tobi136B/co2-wall-sensor/docs/drawing/sheet2_adapters_de.png

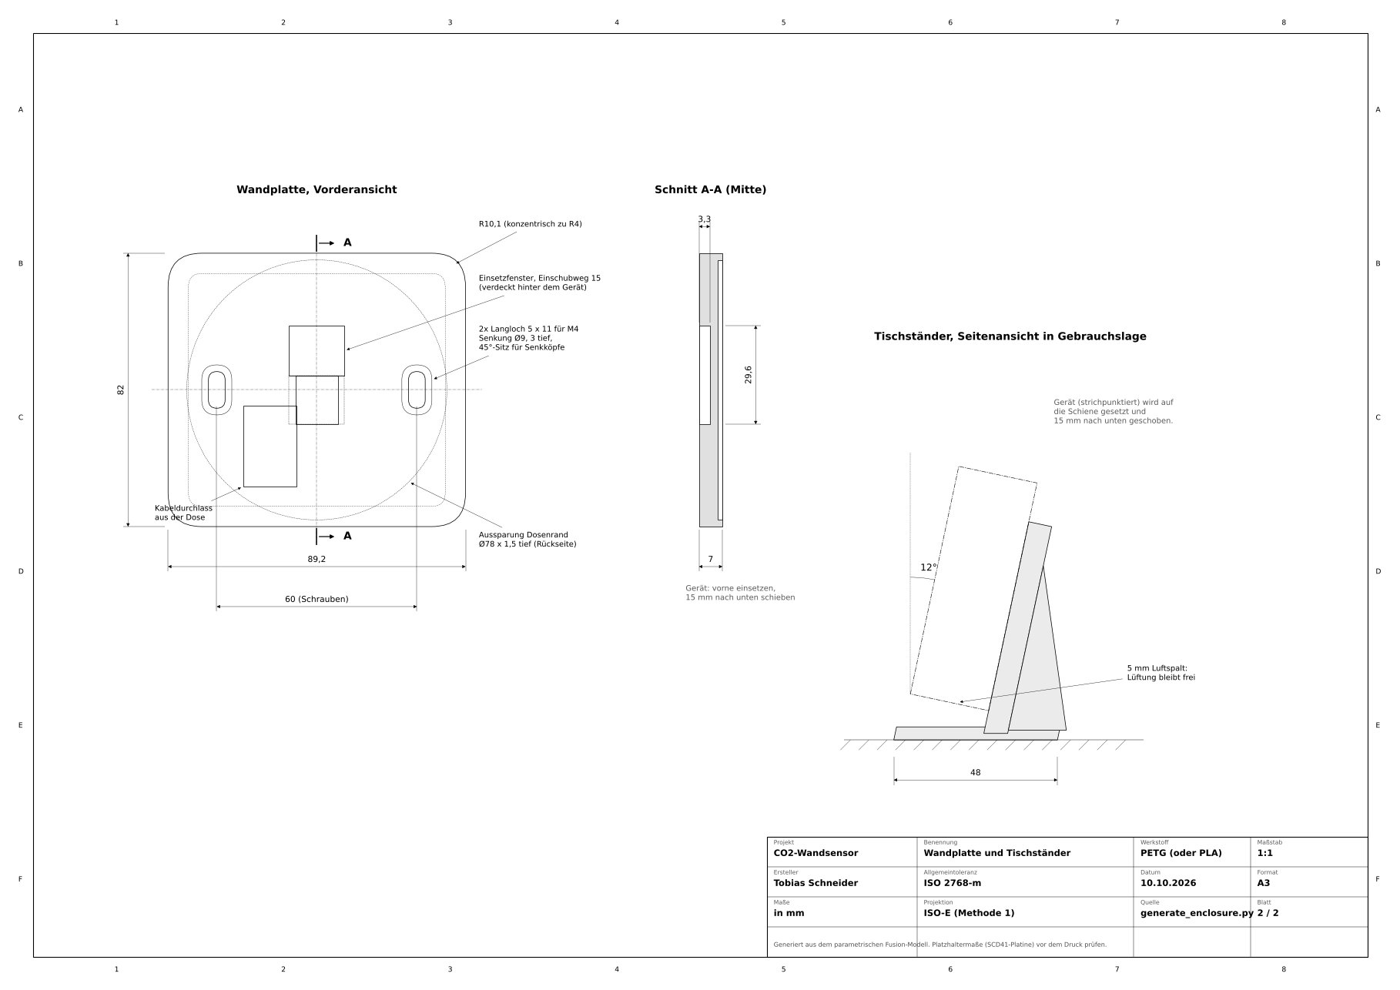
docs/drawing/sheet2_adapters_de.png
