tobi136B/co2-wall-sensor/docs/images/desk_stand.png

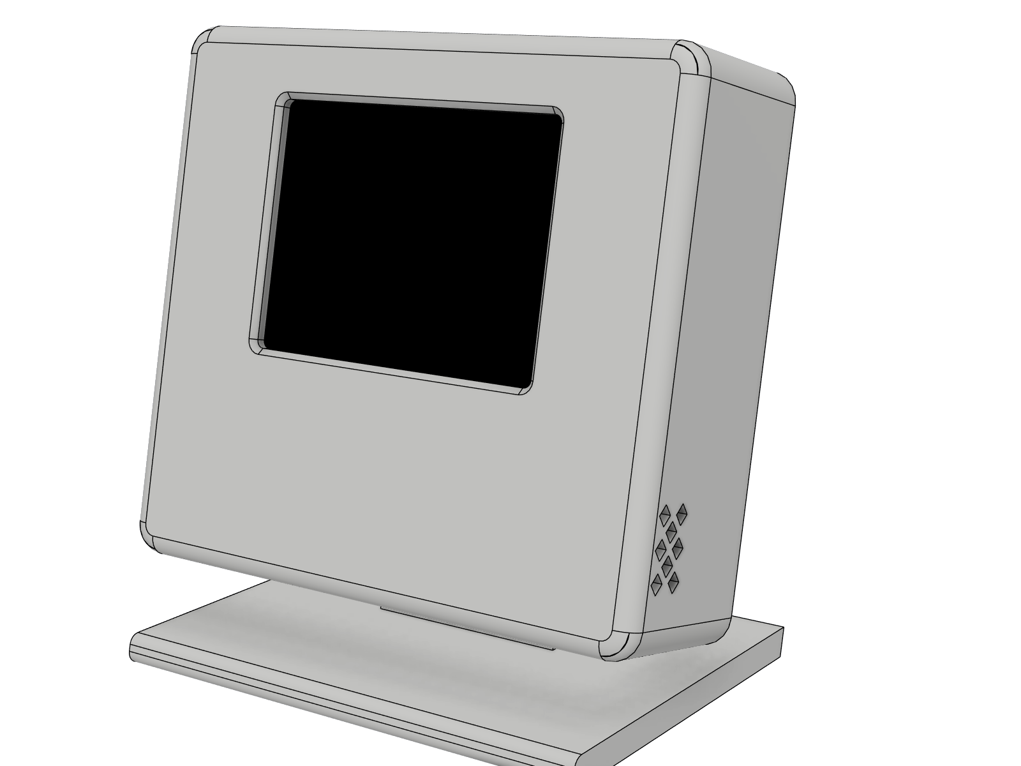
docs/images/desk_stand.png
