tobi136B/co2-wall-sensor/docs/images/hero_wall.png

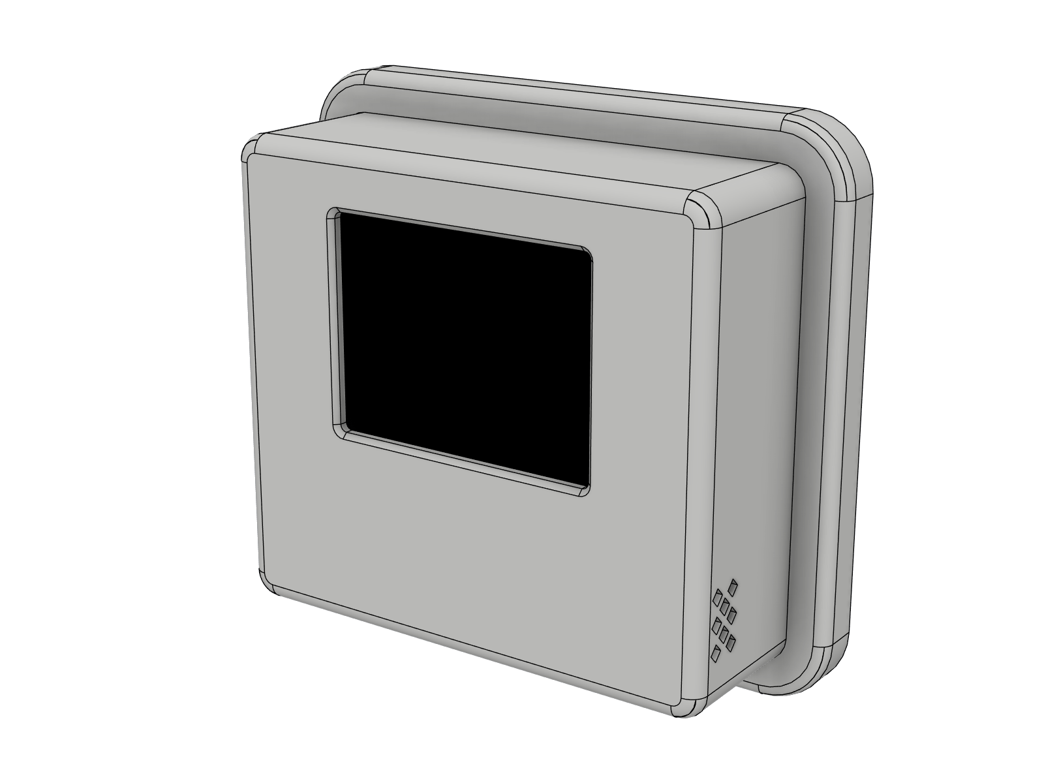
docs/images/hero_wall.png
