tobi136B/co2-wall-sensor/docs/images/sensor_carrier_back.png

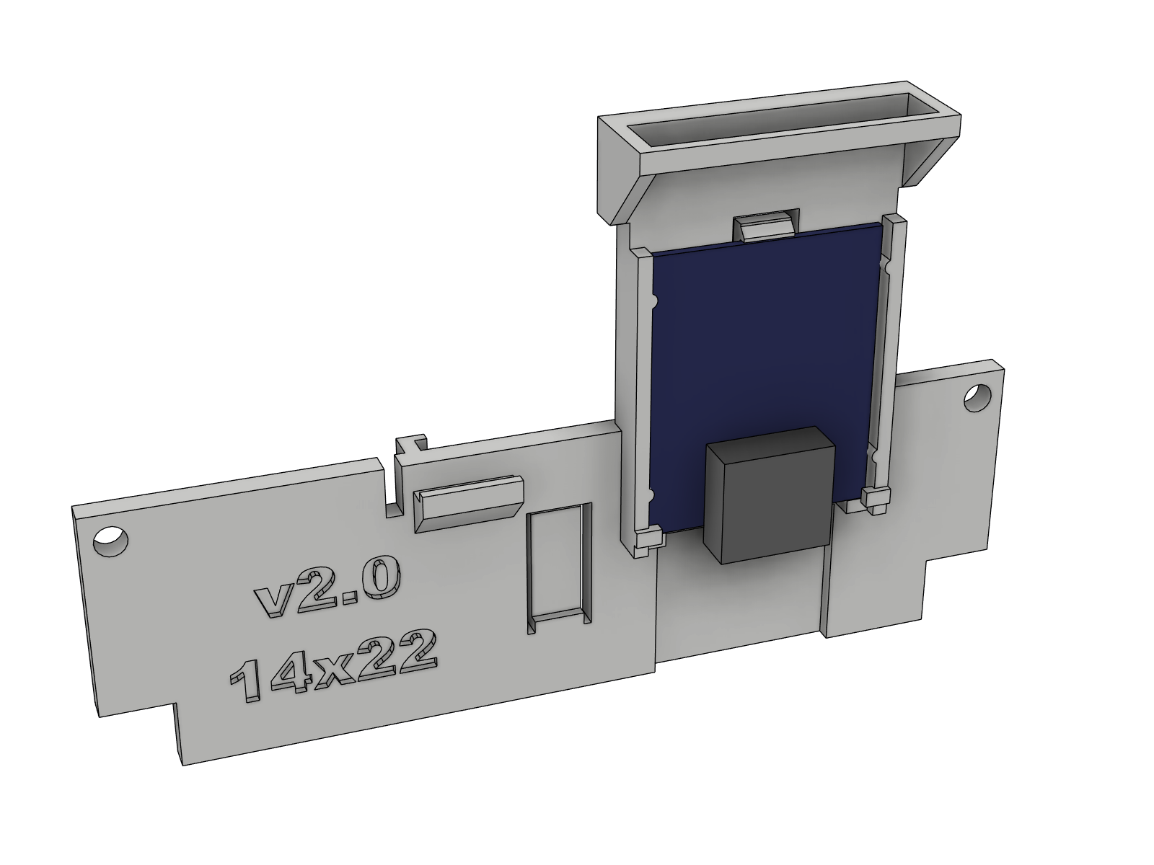
docs/images/sensor_carrier_back.png
