tobi136B/co2-wall-sensor/docs/images/sensor_carrier_front.png

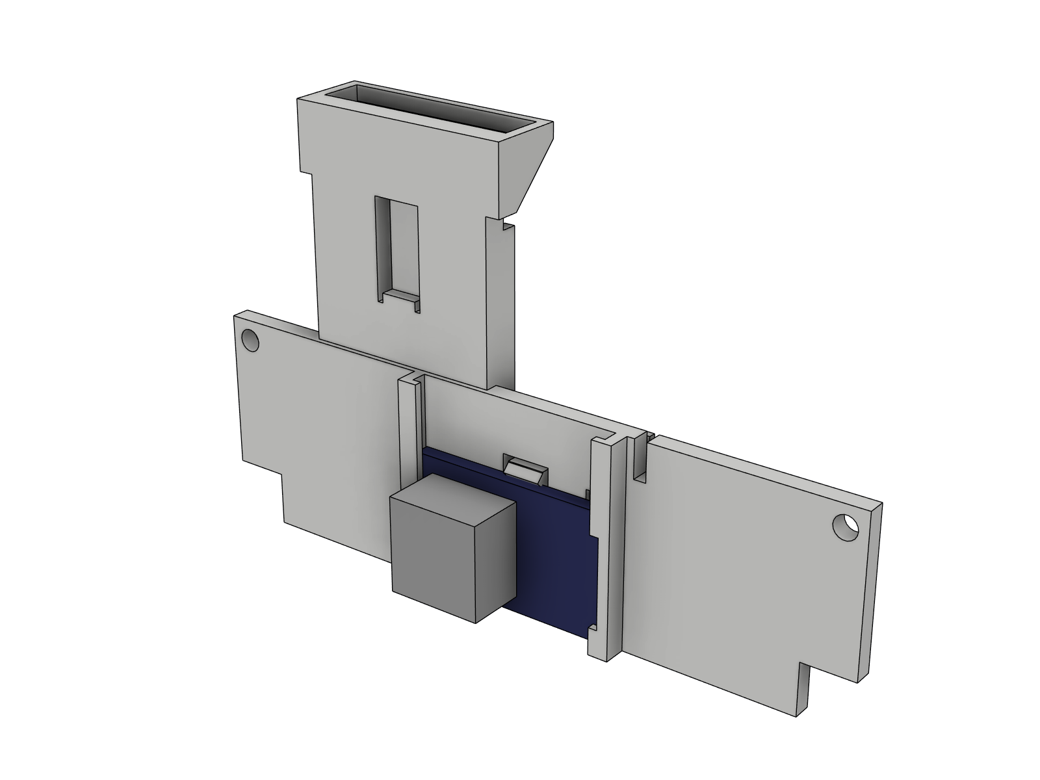
docs/images/sensor_carrier_front.png
