tobi136B/co2-wall-sensor/docs/images/social_preview.png

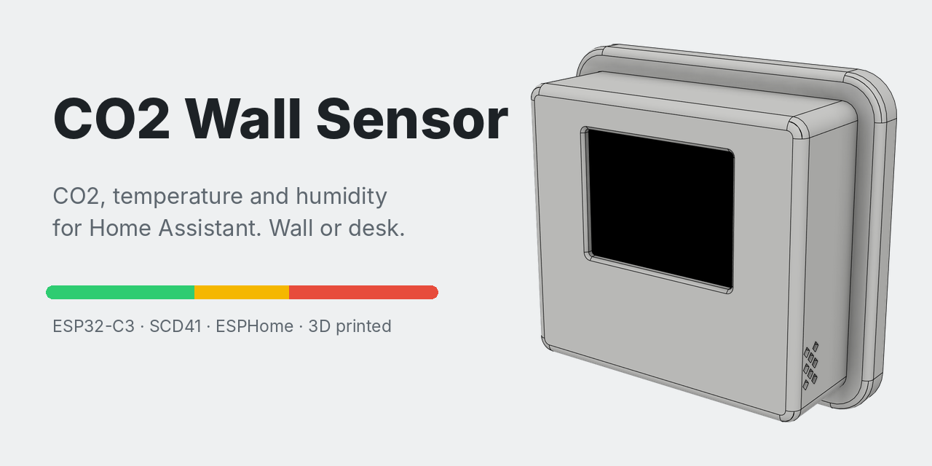
docs/images/social_preview.png
