tobi136B/co2-wall-sensor/tools/bom.py

#!/usr/bin/env python3
"""
Bill of materials: hardware/bom.yaml is the only place for parts, prices and shop links.

The tables in README.md and README.de.md (between the bom markers) and the table on the
project page are generated from it. The format is explained at the top of bom.yaml.

Usage:   python tools/bom.py            (update the README tables)
         python tools/bom.py --check    (exit 1 if a README table is out of date)
"""

from __future__ import annotations

import argparse
import html
import re
import sys
from pathlib import Path

import yaml

ROOT = Path(__file__).resolve().parents[1]
BOM_FILE = ROOT / "hardware" / "bom.yaml"
READMES = {"en": ROOT / "README.md", "de": ROOT / "README.de.md"}
SHOPS = ("aliexpress", "amazon")
KEYS = {"name", "name_de", "qty", "details", "used_for", *SHOPS}
START, END = "<!-- bom:start (generated from hardware/bom.yaml) -->", "<!-- bom:end -->"
HEADER = {
    "en": "| Qty | Part | AliExpress | Amazon.de |\n|----:|------|-----------:|----------:|",
    "de": "| Anz. | Teil | AliExpress | Amazon.de |\n|----:|------|-----------:|----------:|",
}
WORDS_DE = {"pcs": "Stk.", "colours": "Farben", "OD": "AD"}
# shown in a shop column without an offer, so no cell stays empty
ONLY = {
    "en": {"aliexpress": "Amazon only", "amazon": "AliExpress only"},
    "de": {"aliexpress": "nur Amazon", "amazon": "nur AliExpress"},
}


def load() -> list[dict]:
    """All parts, with a readable message for the usual typing errors."""
    try:
        parts = yaml.safe_load(BOM_FILE.read_text(encoding="utf-8"))
    except yaml.YAMLError as e:
        raise SystemExit(f"bom.yaml: {e}") from e
    if not isinstance(parts, list):
        raise SystemExit("bom.yaml: expected a list of parts, each starting with '- name:'")
    return parts


def rows() -> list[dict]:
    """All parts that have at least one shop link."""
    return [p for p in load() if any(p.get(shop) for shop in SHOPS)]


def part_name(part: dict, lang: str) -> str:
    return str(part.get("name_de") or part["name"]) if lang == "de" else str(part["name"])


def price_label(price: object, lang: str) -> tuple[str, str]:
    """'8.99 (2 pcs) ¹' -> ('8.99 € (2 pcs)', ' ¹'); without a price the label is 'Link'."""
    price = f"{price:.2f}" if isinstance(price, (int, float)) else str(price or "").strip()
    note = ""
    if price.endswith("¹"):
        price, note = price[:-1].strip(), " ¹"
    if not price:
        return ("Link", note)
    label = re.sub(r"^(\d+(?:\.\d+)?)", r"\1 €", price)
    if lang == "de":
        label = re.sub(r"(\d)\.(\d)", r"\1,\2", label)
        for en, de in WORDS_DE.items():
            label = re.sub(rf"\b{en}\b", de, label)
    return (label, note)


TOTAL = {
    "en": (
        "Total",
        "one device, each part from this shop if it has it, otherwise from the other; without wire and filament",
    ),
    "de": (
        "Summe",
        "ein Gerät, jedes Teil aus diesem Shop, falls vorhanden, sonst aus dem anderen; ohne Litze und Filament",
    ),
}


def price_value(part: dict, shop: str) -> float | None:
    """First number of a shop price: the amount you pay for the listed offer."""
    offer = part.get(shop)
    if not offer:
        return None
    m = re.match(r"\s*(\d+(?:\.\d+)?)", str(offer.get("price", "")))
    return float(m.group(1)) if m else None


def totals() -> dict[str, float]:
    """Cost of one device per shop column, parts without a quantity (consumables) are left out."""
    out = {}
    for shop in SHOPS:
        other = [s for s in SHOPS if s != shop][0]
        total = 0.0
        for part in rows():
            if not part.get("qty"):
                continue
            value = price_value(part, shop)
            total += value if value is not None else (price_value(part, other) or 0.0)
        out[shop] = round(total, 2)
    out["cheapest"] = round(
        sum(
            min(v for v in (price_value(p, s) for s in SHOPS) if v is not None)
            for p in rows()
            if p.get("qty") and any(price_value(p, s) is not None for s in SHOPS)
        ),
        2,
    )
    return out


def euro(value: float, lang: str) -> str:
    text = f"{value:.2f} €"
    return text.replace(".", ",") if lang == "de" else text


def markdown_table(lang: str) -> str:
    lines = [HEADER[lang]]
    for r in rows():
        cells = []
        for shop in SHOPS:
            if r.get(shop):
                label, note = price_label(r[shop].get("price"), lang)
                cells.append(f"[{label}]({r[shop]['link']}){note}")
            else:
                cells.append(f"*{ONLY[lang][shop]}*")
        lines.append(f"| {r.get('qty', '')} | {part_name(r, lang)} | {cells[0]} | {cells[1]} |")
    t, (word, note) = totals(), TOTAL[lang]
    lines.append(f"| | **{word}** ({note}) | **{euro(t['aliexpress'], lang)}** | **{euro(t['amazon'], lang)}** |")
    return "\n".join(lines)


def html_rows(lang: str) -> str:
    out = []
    for r in rows():
        part = re.sub(r"\*\*(.+?)\*\*", r"<strong>\1</strong>", html.escape(part_name(r, lang)))
        cells = []
        for shop in SHOPS:
            if r.get(shop):
                label, _ = price_label(r[shop].get("price"), lang)
                link = html.escape(r[shop]["link"])
                cells.append(f'<a href="{link}" rel="nofollow noopener">{html.escape(label)}</a>')
            else:
                cells.append(f'<span class="only">{ONLY[lang][shop]}</span>')
        out.append(
            f'          <tr><td class="qty">{r.get("qty", "")}</td><td>{part}</td>'
            f'<td class="shop">{cells[0]}</td><td class="shop">{cells[1]}</td></tr>'
        )
    t, (word, note) = totals(), TOTAL[lang]
    out.append(
        f'          <tr class="total"><td></td><td><strong>{word}</strong> ({html.escape(note)})</td>'
        f'<td class="shop"><strong>{euro(t["aliexpress"], lang)}</strong></td>'
        f'<td class="shop"><strong>{euro(t["amazon"], lang)}</strong></td></tr>'
    )
    return "\n".join(out)


def check_links() -> list[str]:
    """Every part has a name, no unknown keys, every shop block has an https link."""
    errors = []
    for i, part in enumerate(load(), 1):
        name = part.get("name") if isinstance(part, dict) else None
        if not name:
            errors.append(f"bom.yaml: part {i} has no name")
            continue
        for key in set(part) - KEYS:
            errors.append(f"bom.yaml: {name}: unknown key '{key}' (allowed: {', '.join(sorted(KEYS))})")
        for shop in SHOPS:
            offer = part.get(shop)
            if offer is None:
                continue
            link = offer.get("link", "") if isinstance(offer, dict) else ""
            if not str(link).startswith("https://"):
                errors.append(f"bom.yaml: {name}: {shop} needs 'link:' with a complete https link")
    return errors


def updated_readme(lang: str) -> tuple[str, str]:
    path = READMES[lang]
    text = path.read_text(encoding="utf-8")
    pattern = re.compile(re.escape(START) + r".*?" + re.escape(END), re.S)
    if not pattern.search(text):
        raise SystemExit(f"{path.name}: bom markers missing")
    return text, pattern.sub(lambda _: f"{START}\n{markdown_table(lang)}\n{END}", text)


def main() -> int:
    ap = argparse.ArgumentParser(description=__doc__.splitlines()[1])
    ap.add_argument("--check", action="store_true", help="only check, do not write")
    args = ap.parse_args()
    errors = check_links()
    for lang, path in READMES.items():
        if errors:
            break
        old, new = updated_readme(lang)
        if old == new:
            continue
        if args.check:
            errors.append(f"{path.name}: bill of materials is out of date, run python tools/bom.py")
        else:
            path.write_text(new, encoding="utf-8")
            print(f"updated: {path.name}")
    for e in errors:
        print(f"::error::{e}")
    return 1 if errors else 0


if __name__ == "__main__":
    sys.exit(main())
